maks-ushakov/z80-simple-board/variants/minimal_16B/z80-test2-ram-rom-port.kicad_sch

## KiCad design variants/minimal_16B/z80-test2-ram-rom-port.kicad_sch (2024-02-08)

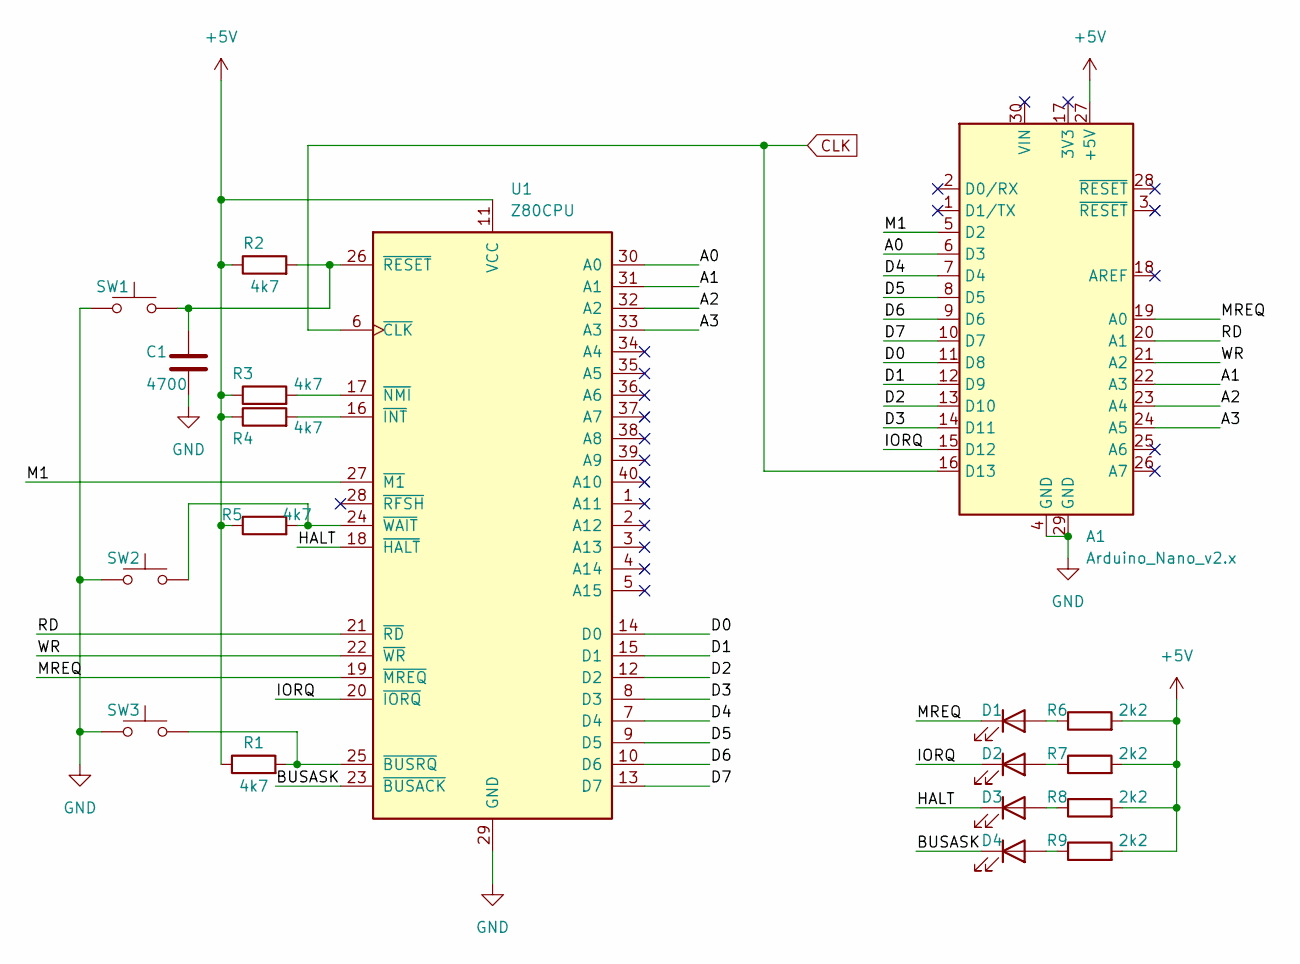
[picture p5: schematic z80-test2-ram-rom-port.kicad_sch]

Parts:
A1: Arduino_Nano_v2.x; Arduino_Nano
C1: 4700
D1, D2, D3, D4: LED
R1, R2, R3, R4, R5: 4k7
R6, R7, R8, R9: 2k2
SW1, SW2, SW3: SW_Push
U1: Z80CPU

Connections:
+5V: A1.27 (+5V), R1.1, R2.1, R3.1, R4.1, R5.1, R6.2, R7.2, R8.2, R9.2, U1.11 (VCC)
A0: A1.6 (D3), U1.30 (A0)
A1: A1.22 (A3), U1.31 (A1)
A2: A1.23 (A4), U1.32 (A2)
A3: A1.24 (A5), U1.33 (A3)
BUSASK: D4.1 (K), U1.23 (~BUSACK)
CLK: A1.16 (D13), U1.6 (~CLK)
D0: A1.11 (D8), U1.14 (D0)
D1: A1.12 (D9), U1.15 (D1)
D2: A1.13 (D10), U1.12 (D2)
D3: A1.14 (D11), U1.8 (D3)
D4: A1.7 (D4), U1.7 (D4)
D5: A1.8 (D5), U1.9 (D5)
D6: A1.9 (D6), U1.10 (D6)
D7: A1.10 (D7), U1.13 (D7)
GND: A1.4 (GND), A1.29 (GND), C1.2, SW1.1, SW2.1, SW3.1, U1.29 (GND)
HALT: D3.1 (K), U1.18 (~HALT)
IORQ: A1.15 (D12), D2.1 (K), U1.20 (~IORQ)
M1: A1.5 (D2), U1.27 (~M1)
MREQ: A1.19 (A0), D1.1 (K), U1.19 (~MREQ)
unnamed: C1.1, R2.2, SW1.2, U1.26 (~RESET)
unnamed: D1.2 (A), R6.1
unnamed: D2.2 (A), R7.1
unnamed: D3.2 (A), R8.1
unnamed: D4.2 (A), R9.1
unnamed: R1.2, SW3.2, U1.25 (~BUSRQ)
unnamed: R3.2, U1.17 (~NMI)
unnamed: R4.2, U1.16 (~INT)
unnamed: R5.2, SW2.2, U1.24 (~WAIT)
RD: A1.20 (A1), U1.21 (~RD)
WR: A1.21 (A2), U1.22 (~WR)
