maks-ushakov/z80-simple-board/variants/minimal_32_64B/step_debug.kicad_sch

## KiCad design variants/minimal_32_64B/step_debug.kicad_sch (2024-04-18)

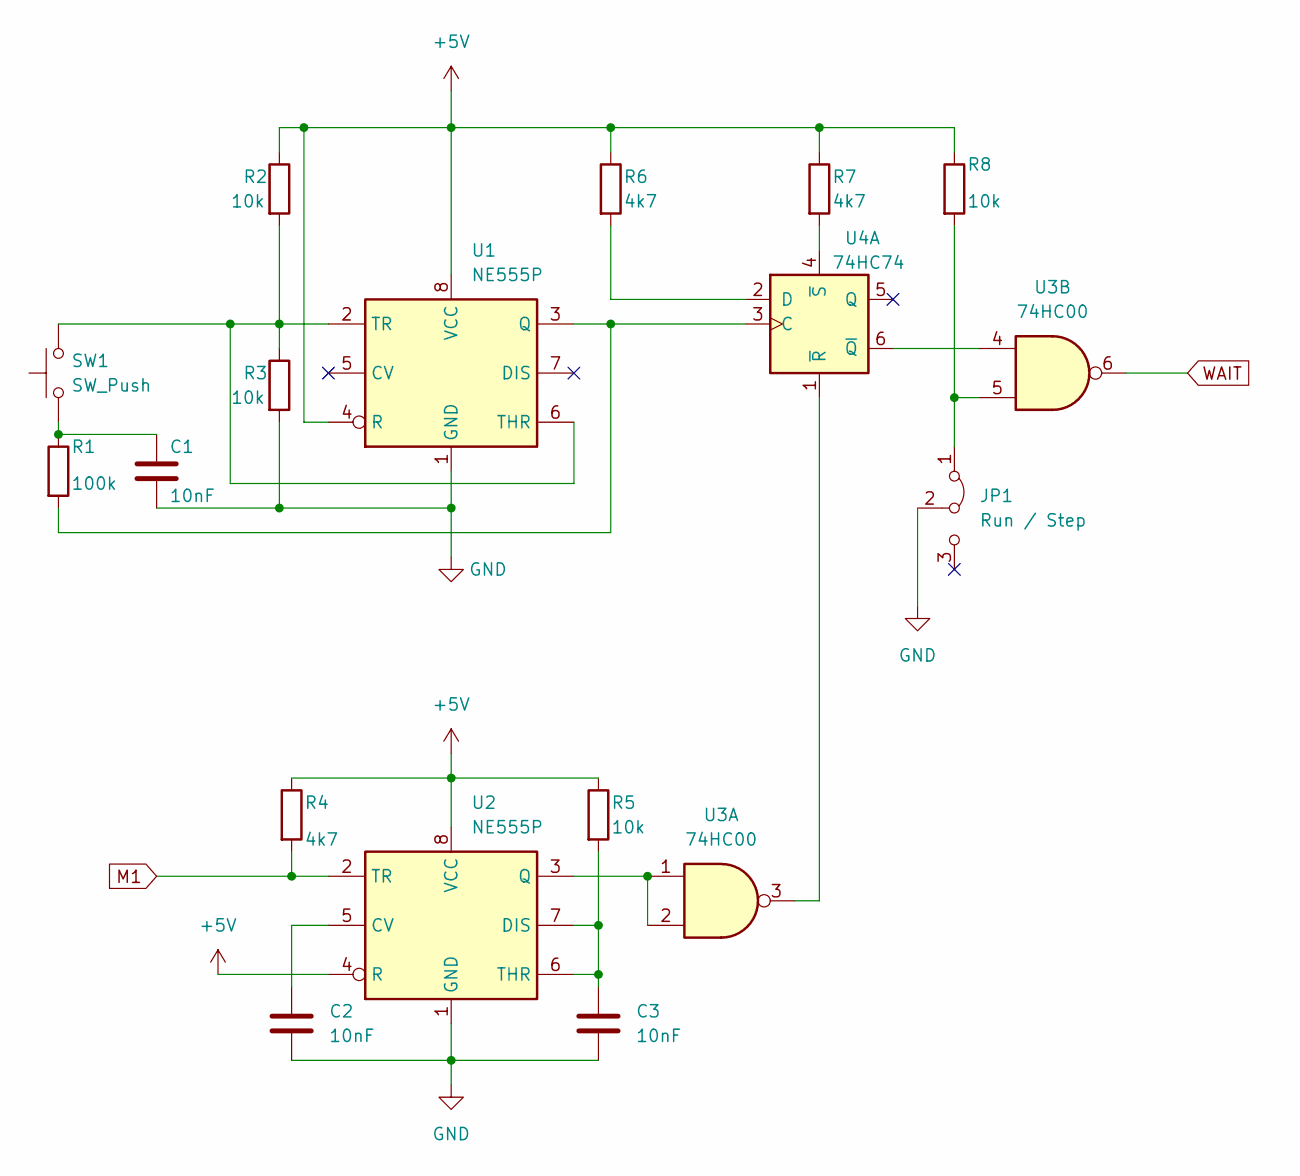
[picture p6: schematic step_debug.kicad_sch]

Parts:
C1, C2, C3: 10nF
JP1: Run / Step
R1: 100k
R2, R3, R5, R8: 10k
R4, R6, R7: 4k7
SW1: SW_Push
U1, U2: NE555P; DIP-8_W7.62mm
U3: 74HC00
U4: 74HC74

Connections:
+5V: R2.1, R4.1, R5.1, R6.1, R7.1, R8.1, U1.4 (R), U1.8 (VCC), U2.4 (R), U2.8 (VCC)
GND: C1.2, C2.2, C3.2, JP1.2 (C), R3.2, U1.1 (GND), U2.1 (GND)
M1: R4.2, U2.2 (TR)
unnamed: C1.1, R1.1, SW1.2
unnamed: C2.1, U2.5 (CV)
unnamed: C3.1, R5.2, U2.6 (THR), U2.7 (DIS)
unnamed: JP1.1 (A), R8.2, U3.5
unnamed: R1.2, U1.3 (Q), U4.3 (C)
unnamed: R2.2, R3.1, SW1.1, U1.2 (TR), U1.6 (THR)
unnamed: R6.2, U4.2 (D)
unnamed: R7.2, U4.4 (~S)
unnamed: U2.3 (Q), U3.1, U3.2
unnamed: U3.3, U4.1 (~R)
unnamed: U3.4, U4.6 (~Q)
WAIT: U3.6
