maks-ushakov/z80-simple-board/variants/minimal_32_64B/z80-Arduino_minmal_32B.kicad_sch

## KiCad design variants/minimal_32_64B/z80-Arduino_minmal_32B.kicad_sch (2024-11-28)

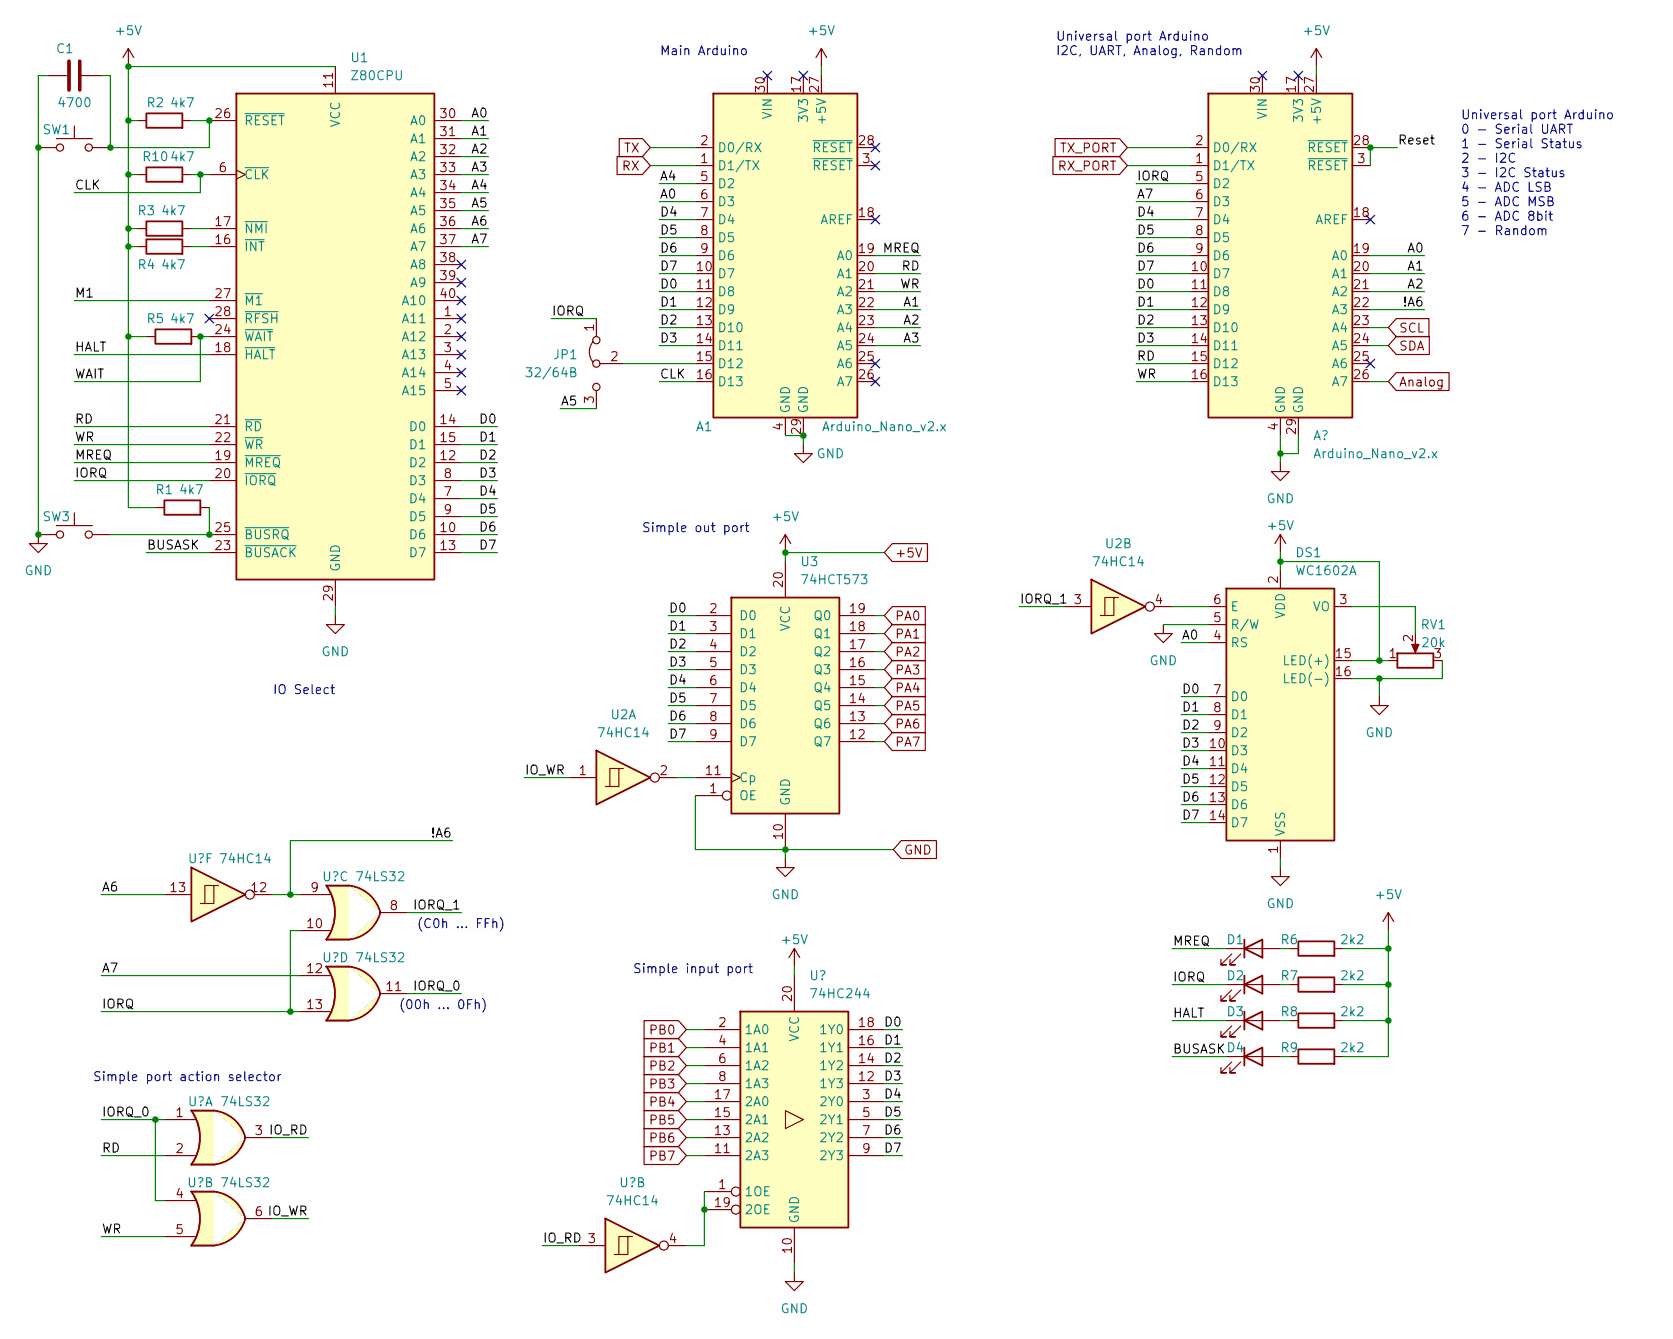
[picture p7: schematic z80-Arduino_minmal_32B.kicad_sch]

Parts:
A1: Arduino_Nano_v2.x; Arduino_Nano
C1: 4700
D1, D2, D3, D4: LED
DS1: WC1602A
JP1: 32/64B
R1, R2, R3, R4, R5, R10: 4k7
R6, R7, R8, R9: 2k2
RV1: 20k
SW1, SW3: SW_Push
U1: Z80CPU
U2: 74HC14
U3: 74HCT573

Connections:
+5V: A1.27 (+5V), DS1.2 (VDD), DS1.15 (LED(+)), R1.1, R2.1, R3.1, R4.1, R5.1, R6.2, R7.2, R8.2, R9.2, R10.1, RV1.1, U1.11 (VCC), U3.20 (VCC)
A0: A1.6 (D3), DS1.4 (RS), U1.30 (A0)
A1: A1.22 (A3), U1.31 (A1)
A2: A1.23 (A4), U1.32 (A2)
A3: A1.24 (A5), U1.33 (A3)
A4: A1.5 (D2), U1.34 (A4)
A5: JP1.3 (B), U1.35 (A5)
A6: U1.36 (A6)
A7: U1.37 (A7)
BUSASK: D4.1 (K), U1.23 (~BUSACK)
CLK: A1.16 (D13), R10.2, U1.6 (~CLK)
D0: A1.11 (D8), DS1.7 (D0), U1.14 (D0), U3.2 (D0)
D1: A1.12 (D9), DS1.8 (D1), U1.15 (D1), U3.3 (D1)
D2: A1.13 (D10), DS1.9 (D2), U1.12 (D2), U3.4 (D2)
D3: A1.14 (D11), DS1.10 (D3), U1.8 (D3), U3.5 (D3)
D4: A1.7 (D4), DS1.11 (D4), U1.7 (D4), U3.6 (D4)
D5: A1.8 (D5), DS1.12 (D5), U1.9 (D5), U3.7 (D5)
D6: A1.9 (D6), DS1.13 (D6), U1.10 (D6), U3.8 (D6)
D7: A1.10 (D7), DS1.14 (D7), U1.13 (D7), U3.9 (D7)
GND: A1.4 (GND), A1.29 (GND), C1.1, DS1.1 (VSS), DS1.5 (R/W), DS1.16 (LED(-)), RV1.3, SW1.1, SW3.1, U1.29 (GND), U3.1 (OE), U3.10 (GND)
HALT: D3.1 (K), U1.18 (~HALT)
IORQ: D2.1 (K), JP1.1 (A), U1.20 (~IORQ)
IORQ_1: U2.3
IO_WR: U2.1
M1: U1.27 (~M1)
MREQ: A1.19 (A0), D1.1 (K), U1.19 (~MREQ)
unnamed: A1.15 (D12), JP1.2 (C)
unnamed: C1.2, R2.2, SW1.2, U1.26 (~RESET)
unnamed: D1.2 (A), R6.1
unnamed: D2.2 (A), R7.1
unnamed: D3.2 (A), R8.1
unnamed: D4.2 (A), R9.1
unnamed: DS1.3 (VO), RV1.2
unnamed: DS1.6 (E), U2.4
unnamed: R1.2, SW3.2, U1.25 (~BUSRQ)
unnamed: R3.2, U1.17 (~NMI)
unnamed: R4.2, U1.16 (~INT)
unnamed: U2.2, U3.11 (Cp)
PA0: U3.19 (Q0)
PA1: U3.18 (Q1)
PA2: U3.17 (Q2)
PA3: U3.16 (Q3)
PA4: U3.15 (Q4)
PA5: U3.14 (Q5)
PA6: U3.13 (Q6)
PA7: U3.12 (Q7)
RD: A1.20 (A1), U1.21 (~RD)
RX: A1.1 (D1/TX)
TX: A1.2 (D0/RX)
WAIT: R5.2, U1.24 (~WAIT)
WR: A1.21 (A2), U1.22 (~WR)

Notes on the sheet:
Simple input port
(00h ... 0Fh)
(C0h ... FFh)
Universal port Arduino I2C, UART, Analog, Random
Simple out port
Universal port Arduino 0 - Serial UART 1 - Serial Status 2 - I2C 3 - I2C Status 4 - ADC LSB 5 - ADC MSB 6 - ADC 8bit 7 - Random
Simple port action selector
IO Select
Main Arduino
