maks-ushakov/z80-simple-board/variants/minimal_32_64B/arduino/z80_Arduino_minimal_32B/CPUMemoryLoader.cpp

#include "Arduino.h"
#include "CPUMemoryLoader.h"
#include "Config.h"

MemoryLoader::MemoryLoader(uint16_t maxAddr) {
  _maxAddr = maxAddr;
};

void MemoryLoader::init(CPUBoard * board) {
  _board = board;
};

uint8_t MemoryLoader::checkAddr(uint16_t addr) {
  return addr < _maxAddr ? 1 : 0;
};

void MemoryLoader::loadChunk(MemoryChunk chunk) {
  uint16_t size = chunk.size;
  uint16_t addr = chunk.startAddress;
  const uint8_t * ptr = chunk.memChunk;
  for (uint16_t i = 0; i < size; i++) {
    setByte(addr + i, pgm_read_byte(ptr + i));
  }
}

#ifndef CPU_MEMORY_MOCKED
uint8_t MemoryLoader::getByte(uint16_t addr) {
   return 0xff;
};

uint8_t MemoryLoader::setByte(uint16_t addr, uint8_t data) {
    return 0;
};
#else

uint8_t mockRAM[] = {
  	0x00, 0x00, 0x00, 0x00, 0x00, 0x00, 0x00, 0x00,
    0x00, 0x00, 0x00, 0x00, 0x00, 0x00, 0x00, 0x00,
    0x00, 0x00, 0x00, 0x00, 0x00, 0x00, 0x00, 0x00,
    0x00, 0x00, 0x00, 0x00, 0x00, 0x00, 0x00, 0x00,
    0x00, 0x00, 0x00, 0x00, 0x00, 0x00, 0x00, 0x00,
    0x00, 0x00, 0x00, 0x00, 0x00, 0x00, 0x00, 0x00,
    0x00, 0x00, 0x00, 0x00, 0x00, 0x00, 0x00, 0x00,
    0x00, 0x00, 0x00, 0x00, 0x00, 0x00, 0x00, 0x00, // 64

#if defined(MEMORY_MOCK_EXTRA_256) or defined(MEMORY_MOCK_EXTRA_512) or defined(MEMORY_MOCK_EXTRA_1024)
    0x00, 0x00, 0x00, 0x00, 0x00, 0x00, 0x00, 0x00,
    0x00, 0x00, 0x00, 0x00, 0x00, 0x00, 0x00, 0x00,
    0x00, 0x00, 0x00, 0x00, 0x00, 0x00, 0x00, 0x00,
    0x00, 0x00, 0x00, 0x00, 0x00, 0x00, 0x00, 0x00,
    0x00, 0x00, 0x00, 0x00, 0x00, 0x00, 0x00, 0x00,
    0x00, 0x00, 0x00, 0x00, 0x00, 0x00, 0x00, 0x00,
    0x00, 0x00, 0x00, 0x00, 0x00, 0x00, 0x00, 0x00,
    0x00, 0x00, 0x00, 0x00, 0x00, 0x00, 0x00, 0x00, // 128

    0x00, 0x00, 0x00, 0x00, 0x00, 0x00, 0x00, 0x00,
    0x00, 0x00, 0x00, 0x00, 0x00, 0x00, 0x00, 0x00,
    0x00, 0x00, 0x00, 0x00, 0x00, 0x00, 0x00, 0x00,
    0x00, 0x00, 0x00, 0x00, 0x00, 0x00, 0x00, 0x00,
    0x00, 0x00, 0x00, 0x00, 0x00, 0x00, 0x00, 0x00,
    0x00, 0x00, 0x00, 0x00, 0x00, 0x00, 0x00, 0x00,
    0x00, 0x00, 0x00, 0x00, 0x00, 0x00, 0x00, 0x00,
    0x00, 0x00, 0x00, 0x00, 0x00, 0x00, 0x00, 0x00,
    0x00, 0x00, 0x00, 0x00, 0x00, 0x00, 0x00, 0x00,
    0x00, 0x00, 0x00, 0x00, 0x00, 0x00, 0x00, 0x00,
    0x00, 0x00, 0x00, 0x00, 0x00, 0x00, 0x00, 0x00,
    0x00, 0x00, 0x00, 0x00, 0x00, 0x00, 0x00, 0x00,
    0x00, 0x00, 0x00, 0x00, 0x00, 0x00, 0x00, 0x00,
    0x00, 0x00, 0x00, 0x00, 0x00, 0x00, 0x00, 0x00,
    0x00, 0x00, 0x00, 0x00, 0x00, 0x00, 0x00, 0x00,
    0x00, 0x00, 0x00, 0x00, 0x00, 0x00, 0x00, 0x00, // 256
  #endif
  #if defined(MEMORY_MOCK_EXTRA_512) or defined(MEMORY_MOCK_EXTRA_1024)
  	0x00, 0x00, 0x00, 0x00, 0x00, 0x00, 0x00, 0x00,
    0x00, 0x00, 0x00, 0x00, 0x00, 0x00, 0x00, 0x00,
    0x00, 0x00, 0x00, 0x00, 0x00, 0x00, 0x00, 0x00,
    0x00, 0x00, 0x00, 0x00, 0x00, 0x00, 0x00, 0x00,
    0x00, 0x00, 0x00, 0x00, 0x00, 0x00, 0x00, 0x00,
    0x00, 0x00, 0x00, 0x00, 0x00, 0x00, 0x00, 0x00,
    0x00, 0x00, 0x00, 0x00, 0x00, 0x00, 0x00, 0x00,
    0x00, 0x00, 0x00, 0x00, 0x00, 0x00, 0x00, 0x00,
    0x00, 0x00, 0x00, 0x00, 0x00, 0x00, 0x00, 0x00,
    0x00, 0x00, 0x00, 0x00, 0x00, 0x00, 0x00, 0x00,
    0x00, 0x00, 0x00, 0x00, 0x00, 0x00, 0x00, 0x00,
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

};

uint8_t MemoryLoader::setBlock(uint16_t addr, uint8_t* buffer, uint16_t size, bool pgmem) {
  if (pgmem == 1) {
    return 0;
  }
  for(int i = 0; i < size; i++) {
    mockRAM[addr + i] = buffer[i];
  }
  return 0;
};
#endif
