maks-ushakov/z80-simple-board/variants/minimal_32_64B/arduino/z80_Arduino_minimal_32B/CPU_Board.h

#ifndef CPU_BOARD_H_
#define CPU_BOARD_H_ 100

#define CLK_PIN 13
#define IN_M1 2
#define IN_MREQ A0
#define IN_IORQ 12
#define IN_RD A1
#define IN_WR A2
#define IN_A0 3
#define IN_A1 A3
#define IN_A2 A4
#define IN_A3 A5
#define IN_A4 2
#define IN_A5 12

#define F_HIGHT 1
#define F_1M    1
#define F_500K  2
#define F_250K  4
#define F_100K  10
#define F_50K   20
#define F_1K    1000
#define F_500   2000
#define F_250   4000
#define F_100   10000
#define F_10    100000
#define F_1     1000000

class CPUBoard 
{
  public:
    CPUBoard();
    void init();
    void tick(unsigned long currentMillis);
    uint8_t getAddr();
    void setData(uint8_t data);
    uint8_t getData();
    void setAsDataInput();
    void setClock(long);

  private:
    uint8_t control_pins[8], addr_pins[16];
    long _interval = 100;           // interval at which to change CLK state (milliseconds)
    // Variables will change:
    uint8_t _clk_State = LOW;
    long previousMillis = 0;        // will store last time CLK was updated
    // the follow variables is a long because the time, measured in miliseconds,
    // will quickly become a bigger number than can be stored in an int.
};

#endif
